gruvin/gswitch18/hardware/gswitch18.sch

## KiCad design hardware/gswitch18.sch (2012-09-26)

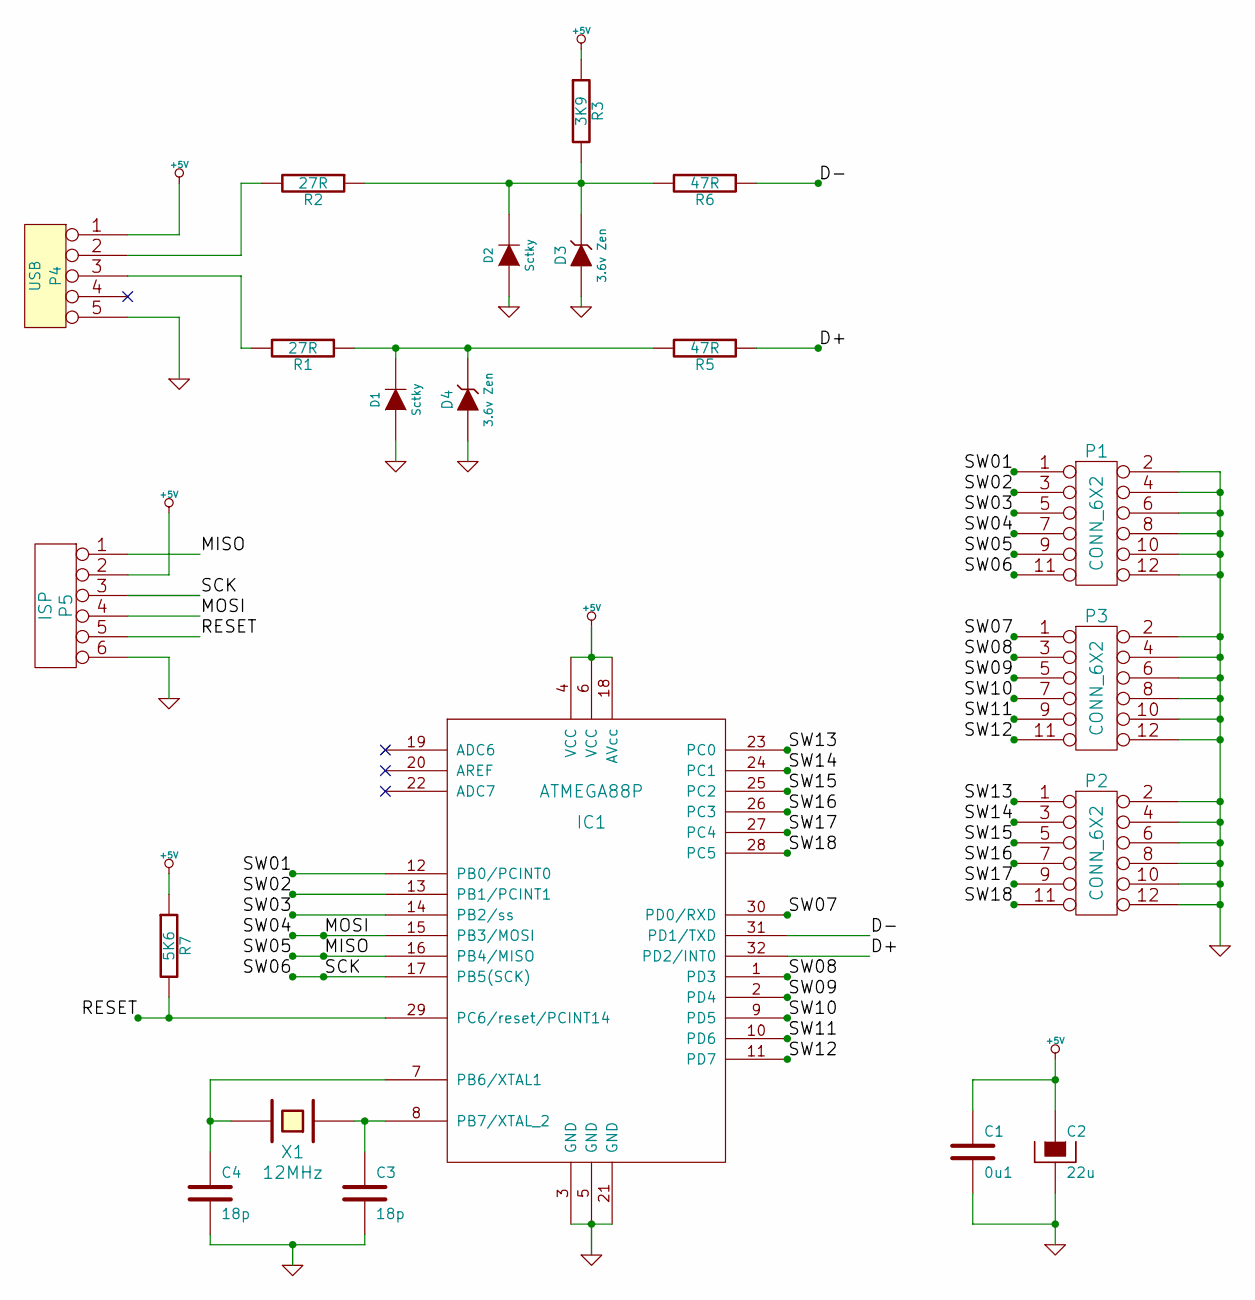
[picture p6: schematic gswitch18.sch]

Parts:
C1: 0u1
C2: 22u
C3, C4: 18p
D1, D2: Sctky
D3, D4: 3.6v Zen
IC1: ATMEGA88P
P1, P2, P3: CONN_6X2
P4: USB
P5: ISP
R1, R2: 27R
R3: 3K9
R5, R6: 47R
R7: 5K6
X1: 12MHz

Connections:
+5V: C1.1, C2.1, IC1.4 (VCC), IC1.6 (VCC), IC1.18 (AVcc), P4.1, P5.2, R3.1, R7.1
D+: IC1.32 (PD2/INT0), R5.1
D-: IC1.31 (PD1/TXD), R6.1
GND: C1.2, C2.2, C3.2, C4.2, D1.1 (A), D2.1 (A), D3.1 (A), D4.1 (A), IC1.3 (GND), IC1.5 (GND), IC1.21 (GND), P1.2, P1.4, P1.6, P1.8, P1.10, P1.12, P2.2, P2.4, P2.6, P2.8, P2.10, P2.12, P3.2, P3.4, P3.6, P3.8, P3.10, P3.12, P4.5, P5.6
MISO: IC1.16 (PB4/MISO), P1.9, P5.1
MOSI: IC1.15 (PB3/MOSI), P1.7, P5.4
unnamed: C3.1, IC1.8 (PB7/XTAL_2), X1.1
unnamed: C4.1, IC1.7 (PB6/XTAL1), X1.2
unnamed: D1.2 (K), D4.2 (K), R1.1, R5.2
unnamed: D2.2 (K), D3.2 (K), R2.1, R3.2, R6.2
unnamed: P4.2, R2.2
unnamed: P4.3, R1.2
RESET: IC1.29 (PC6/reset/PCINT14), P5.5, R7.2
SCK: IC1.17 (PB5(SCK)), P1.11, P5.3
SW01: IC1.12 (PB0/PCINT0), P1.1
SW02: IC1.13 (PB1/PCINT1), P1.3
SW03: IC1.14 (PB2/ss), P1.5
SW07: IC1.30 (PD0/RXD), P3.1
SW08: IC1.1 (PD3), P3.3
SW09: IC1.2 (PD4), P3.5
SW10: IC1.9 (PD5), P3.7
SW11: IC1.10 (PD6), P3.9
SW12: IC1.11 (PD7), P3.11
SW13: IC1.23 (PC0), P2.1
SW14: IC1.24 (PC1), P2.3
SW15: IC1.25 (PC2), P2.5
SW16: IC1.26 (PC3), P2.7
SW17: IC1.27 (PC4), P2.9
SW18: IC1.28 (PC5), P2.11
